andreasb242/Libreductioner/Measure/LandroidWorx/Inside/00original.png

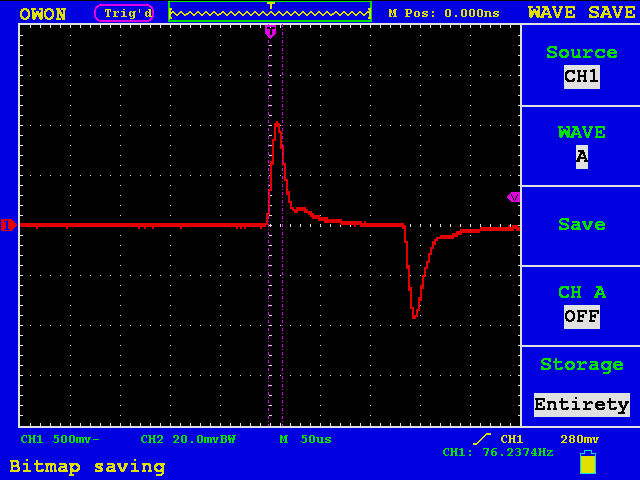
Measure/LandroidWorx/Inside/00original.png
