andreasb242/Libreductioner/Measure/LandroidWorx/Inside/01.png

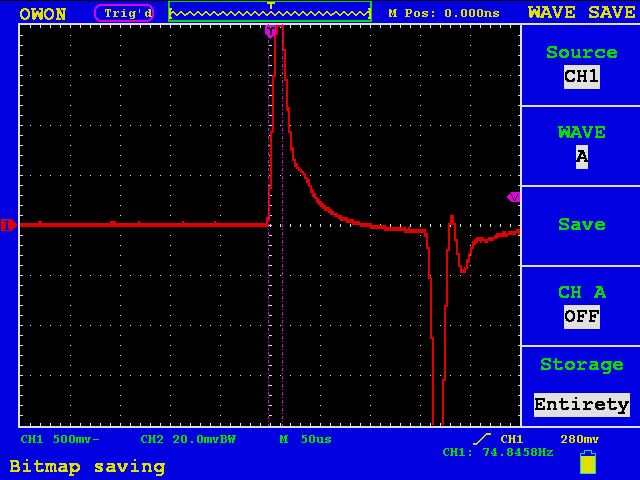
Measure/LandroidWorx/Inside/01.png
