andreasb242/Libreductioner/Measure/LandroidWorx/Outside/01.png

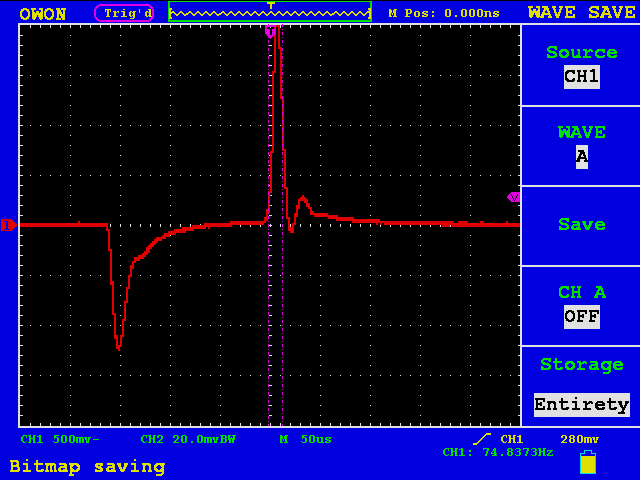
Measure/LandroidWorx/Outside/01.png
