andreasb242/Libreductioner/Measure/LandroidWorx/Timing/00B-original.png

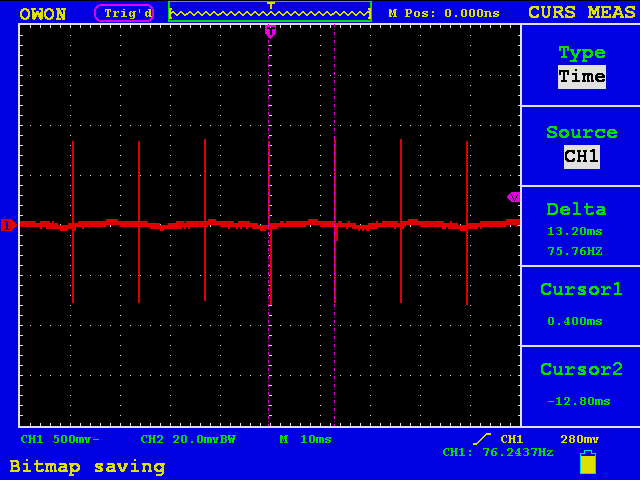
Measure/LandroidWorx/Timing/00B-original.png
